MartinLautaroGimenez/estacion-meteorologica-estatica/models/Anemometer/images/4ff4661ae505d6dd8fcebf4c1d2a20cf.png

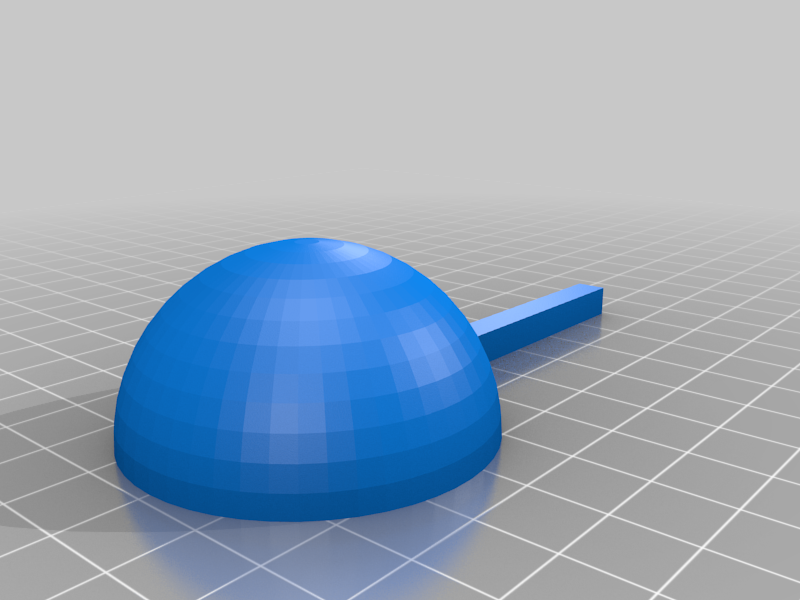
models/Anemometer/images/4ff4661ae505d6dd8fcebf4c1d2a20cf.png
