MartinLautaroGimenez/estacion-meteorologica-estatica/models/Anemometer/images/28f046effea293050f0cdabce47c510c.png

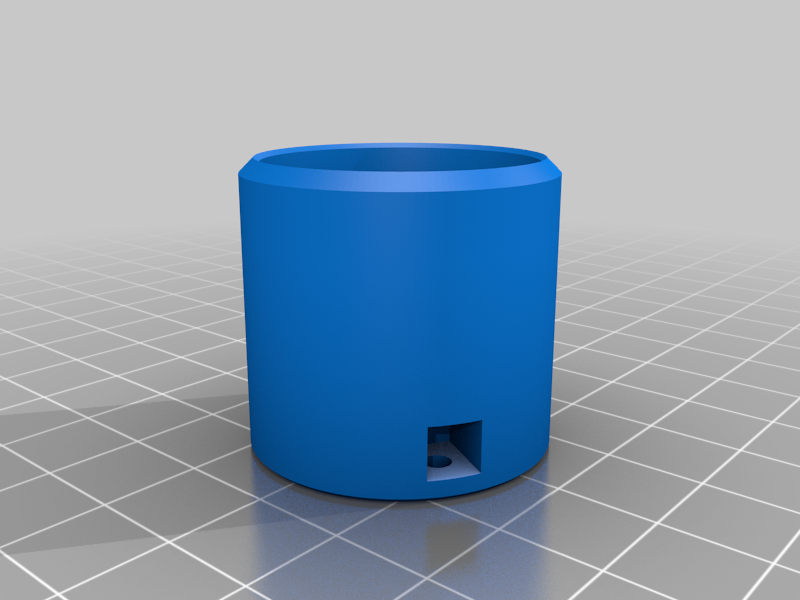
models/Anemometer/images/28f046effea293050f0cdabce47c510c.png
