MartinLautaroGimenez/estacion-meteorologica-estatica/models/Anemometer/images/anem.jpg

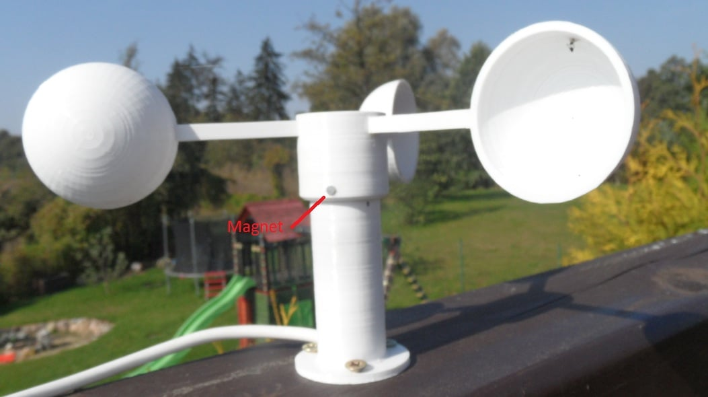
models/Anemometer/images/anem.jpg
