MartinLautaroGimenez/estacion-meteorologica-estatica/models/Anemometer/images/d6e86a1413bca8652d84cd858a84a04f.png

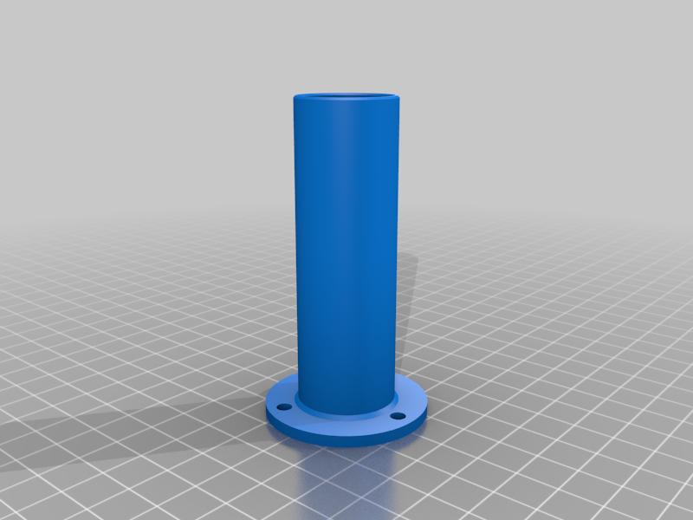
models/Anemometer/images/d6e86a1413bca8652d84cd858a84a04f.png
