MartinLautaroGimenez/estacion-meteorologica-estatica/models/Anemometer/images/hall_sensor.jpg

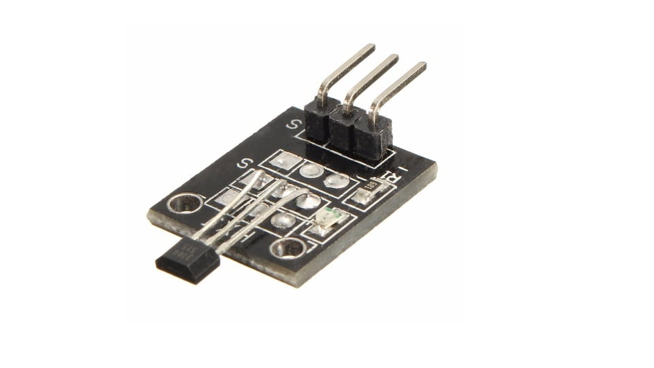
models/Anemometer/images/hall_sensor.jpg
