MartinLautaroGimenez/estacion-meteorologica-estatica/models/Anemometer/images/magnet.jpg

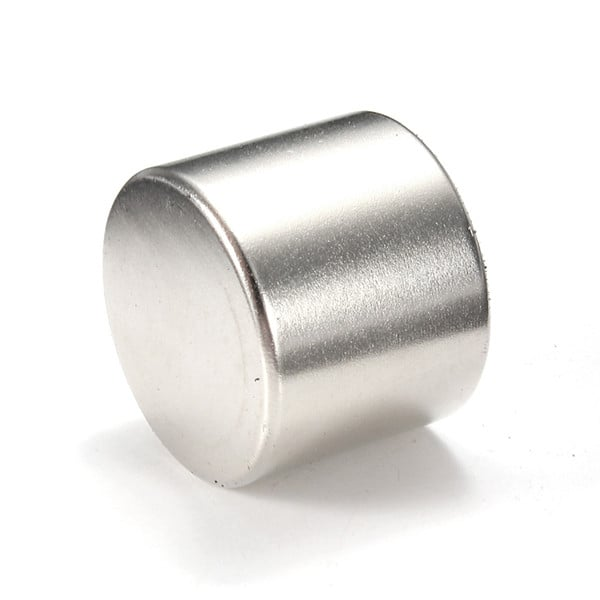
models/Anemometer/images/magnet.jpg
