MartinLautaroGimenez/estacion-meteorologica-estatica/Web/frontend/images/2025.jpg

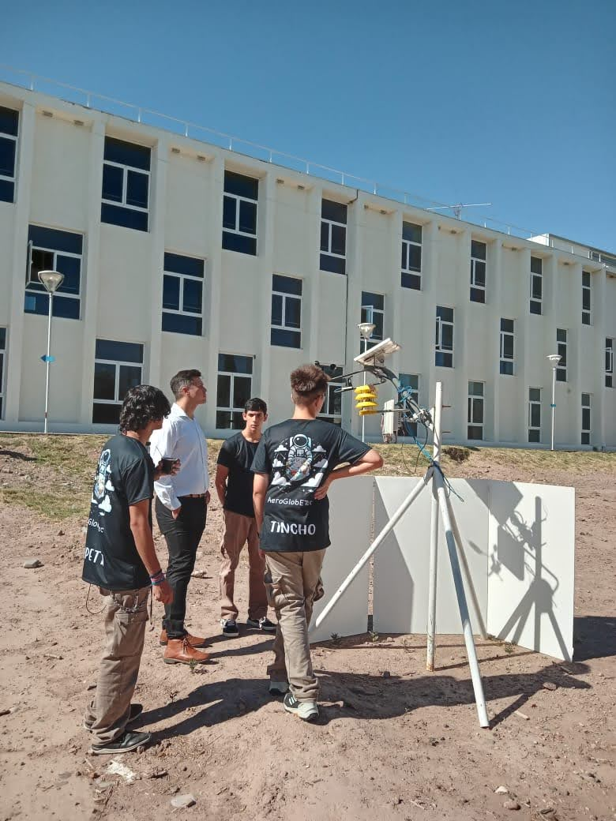
Web/frontend/images/2025.jpg
