MartinLautaroGimenez/estacion-meteorologica-estatica/Web/frontend/images/2025.png

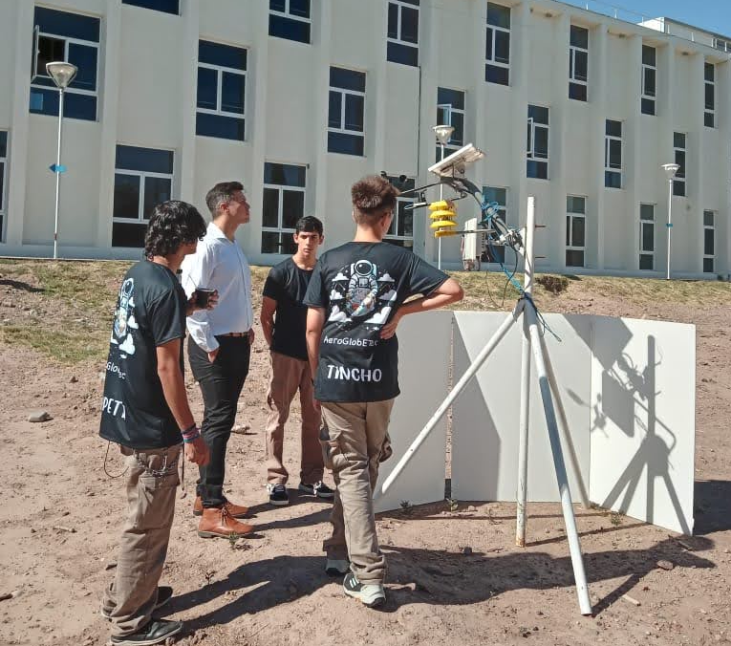
Web/frontend/images/2025.png
