MartinLautaroGimenez/estacion-meteorologica-estatica/Web/frontend/images/cate2023.jpeg

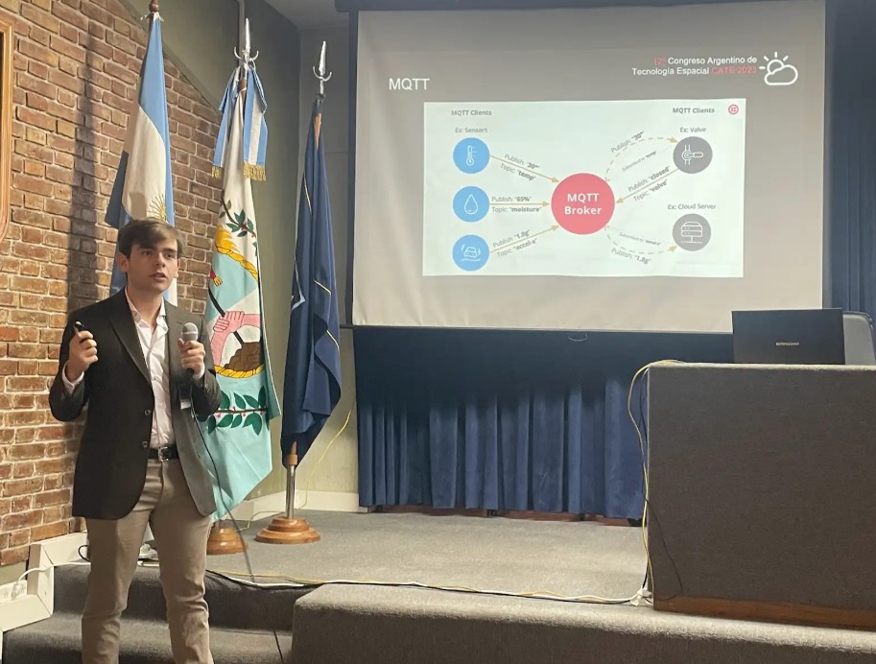
Web/frontend/images/cate2023.jpeg
