MartinLautaroGimenez/estacion-meteorologica-estatica/Web/frontend/images/eclipse.jpg

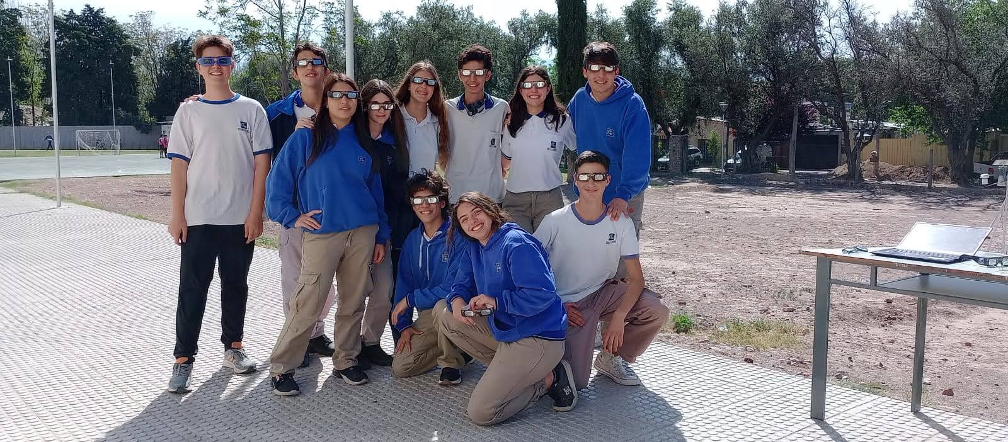
Web/frontend/images/eclipse.jpg
