MartinLautaroGimenez/estacion-meteorologica-estatica/Web/frontend/images/eme.jpeg

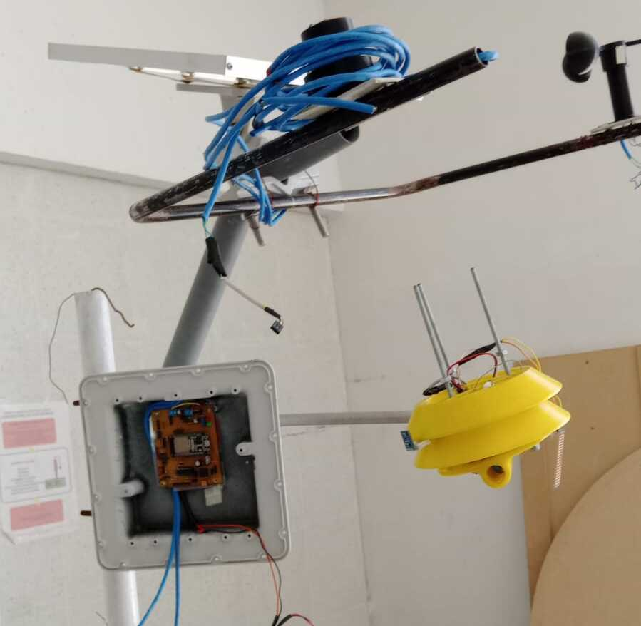
Web/frontend/images/eme.jpeg
