MartinLautaroGimenez/estacion-meteorologica-estatica/Web/frontend/images/eme.jpg

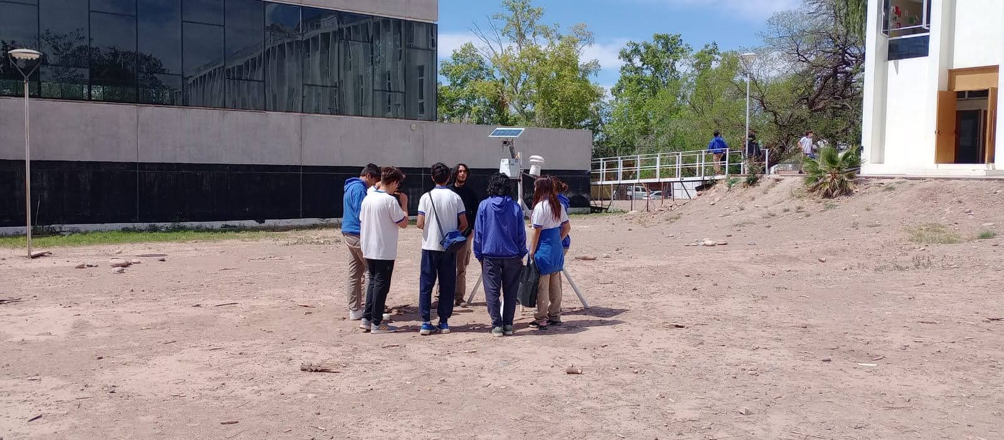
Web/frontend/images/eme.jpg
