MartinLautaroGimenez/estacion-meteorologica-estatica/Web/frontend/images/emebasica.jpeg

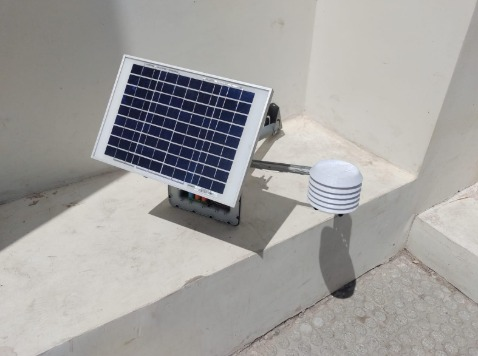
Web/frontend/images/emebasica.jpeg
