MartinLautaroGimenez/estacion-meteorologica-estatica/Web/frontend/images/emecompleta.jpeg

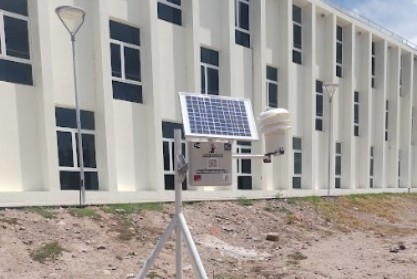
Web/frontend/images/emecompleta.jpeg
