MartinLautaroGimenez/estacion-meteorologica-estatica/Web/frontend/images/emm.jpeg

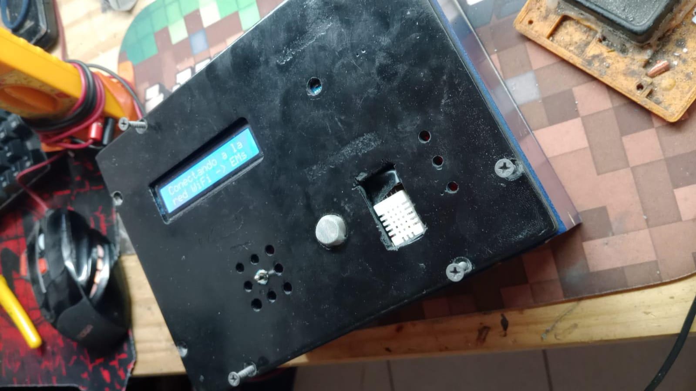
Web/frontend/images/emm.jpeg
