MartinLautaroGimenez/estacion-meteorologica-estatica/Web/frontend/images/heredar.jpg

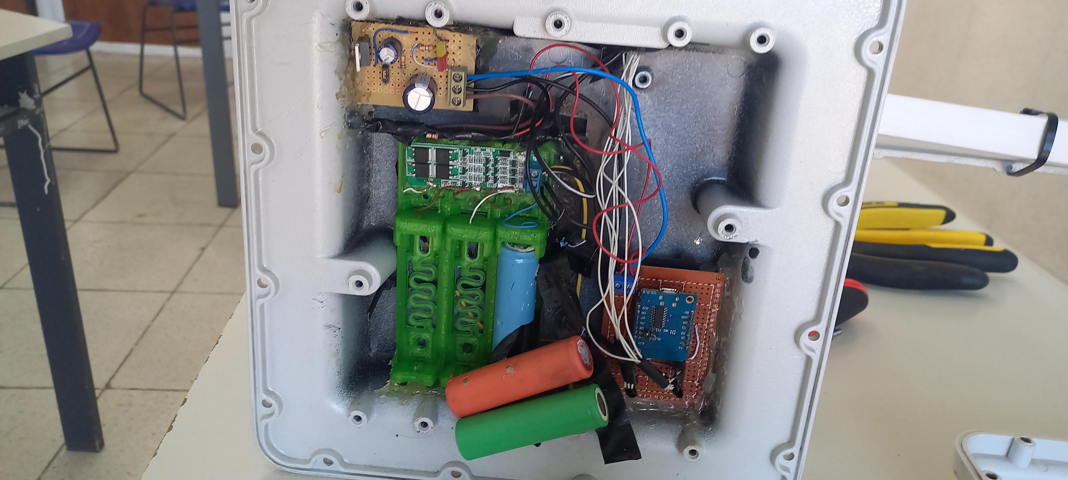
Web/frontend/images/heredar.jpg
