MartinLautaroGimenez/estacion-meteorologica-estatica/Web/frontend/images/nuestraeme.png

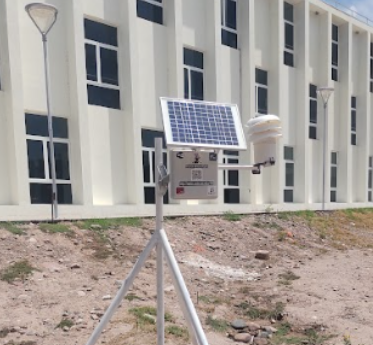
Web/frontend/images/nuestraeme.png
