MartinLautaroGimenez/estacion-meteorologica-estatica/Web/frontend/images/PIERRE.png

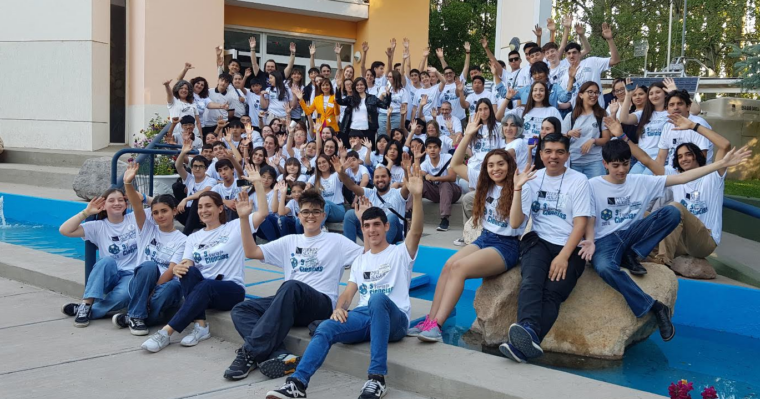
Web/frontend/images/PIERRE.png
