MartinLautaroGimenez/estacion-meteorologica-estatica/Web/frontend/images/sj.jpg

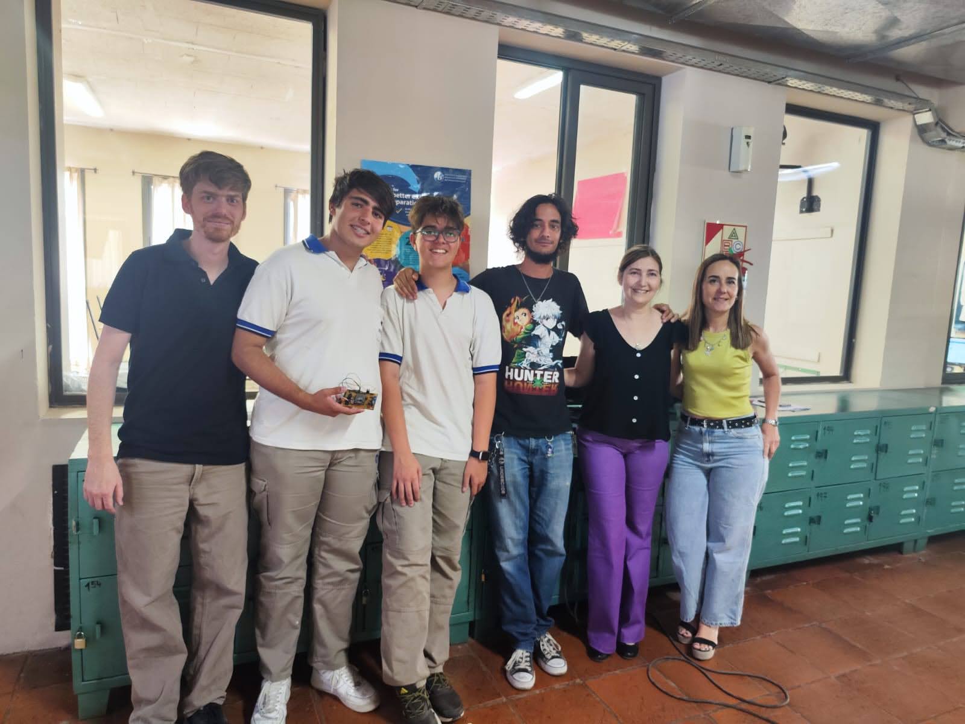
Web/frontend/images/sj.jpg
