MartinLautaroGimenez/estacion-meteorologica-estatica/Web/frontend/images/team/emecompleta.jpeg

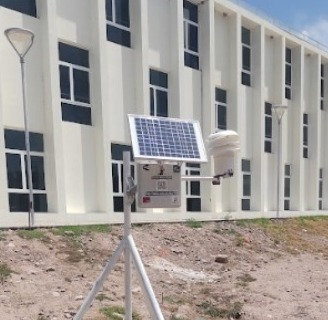
Web/frontend/images/team/emecompleta.jpeg
