MartinLautaroGimenez/estacion-meteorologica-estatica/Web/frontend/images/team/ivo.jpg

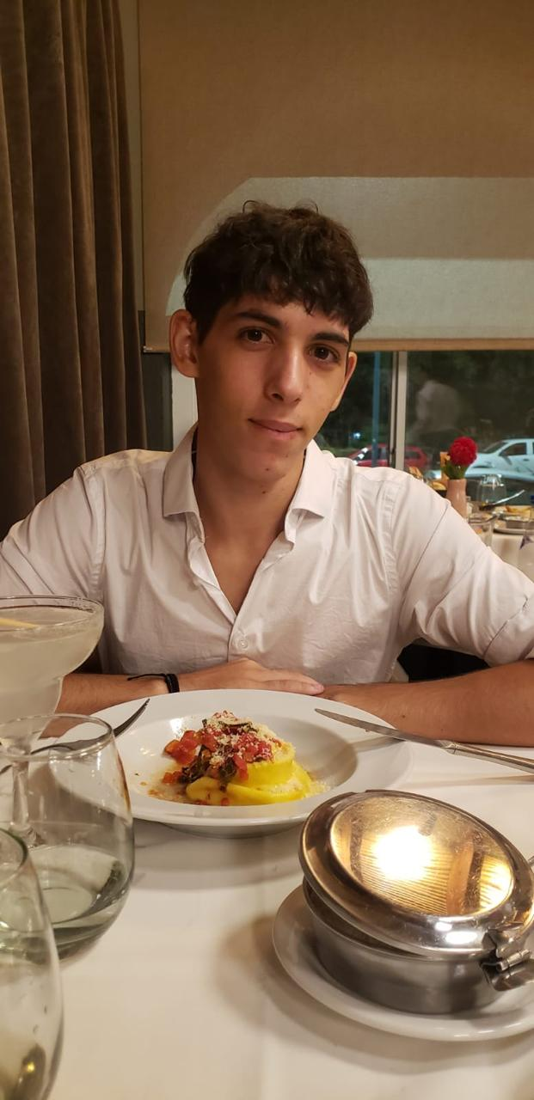
Web/frontend/images/team/ivo.jpg
