MartinLautaroGimenez/estacion-meteorologica-estatica/Web/frontend/images/team/Luis.jpg

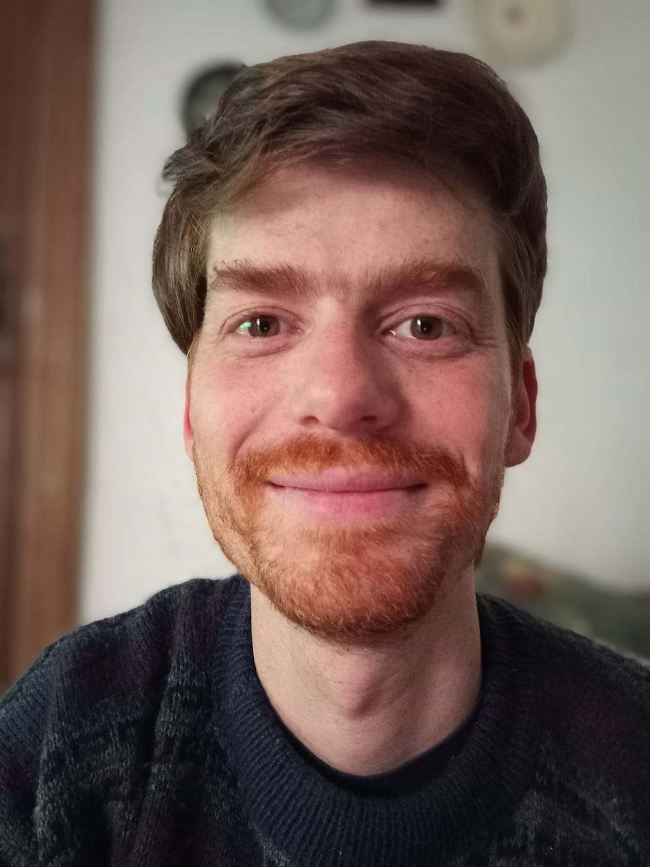
Web/frontend/images/team/Luis.jpg
