MartinLautaroGimenez/estacion-meteorologica-estatica/Web/frontend/images/team/mario.jpg

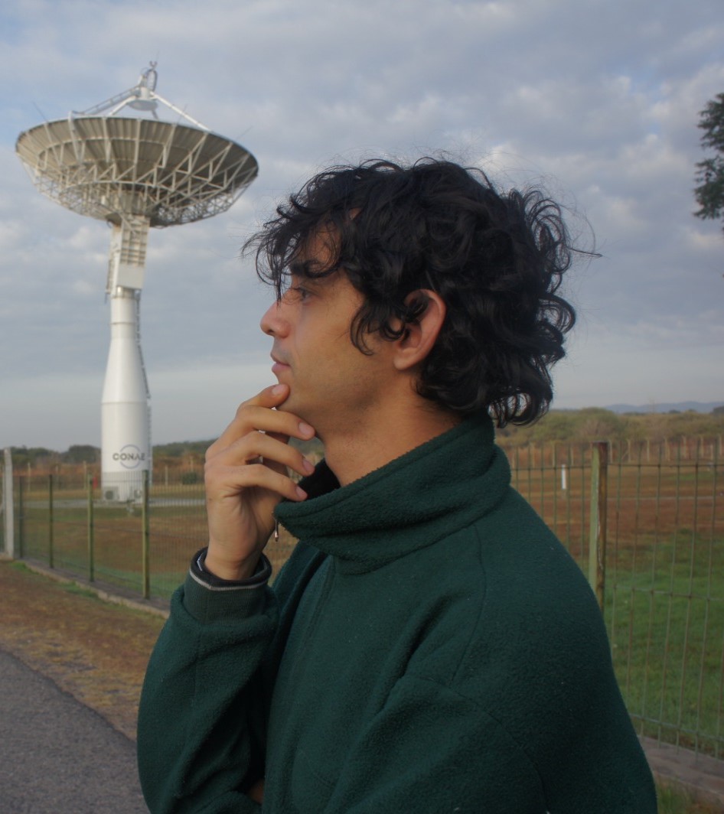
Web/frontend/images/team/mario.jpg
