MartinLautaroGimenez/estacion-meteorologica-estatica/Web/frontend/images/team/martin.jpg

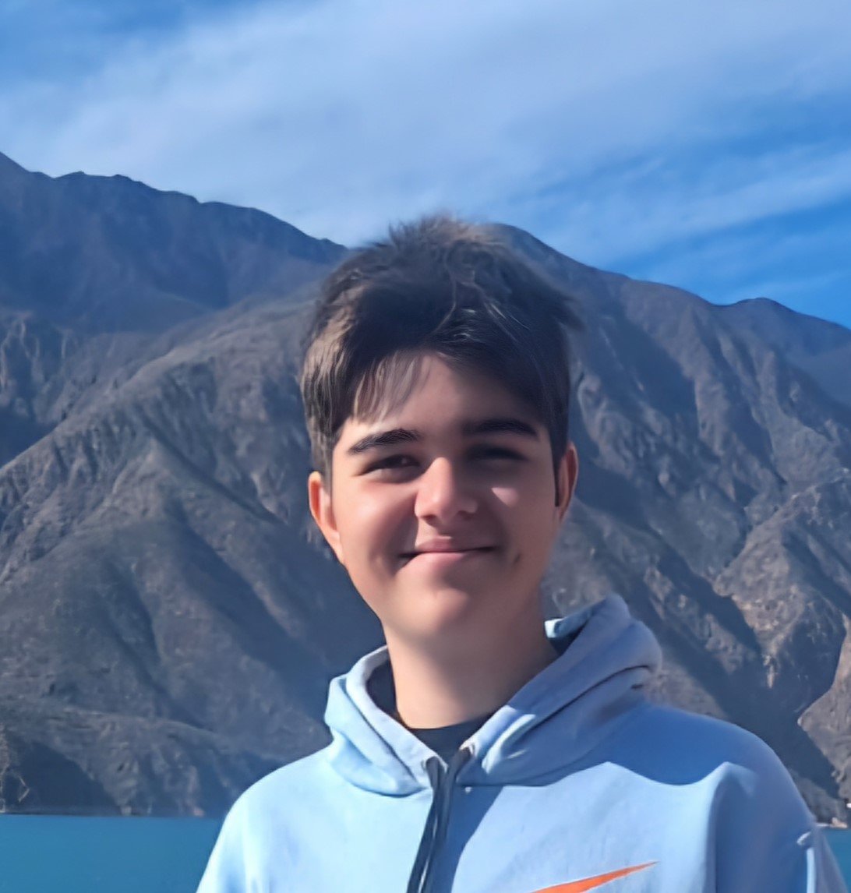
Web/frontend/images/team/martin.jpg
