MartinLautaroGimenez/estacion-meteorologica-estatica/Web/frontend/images/tucuman.jpg

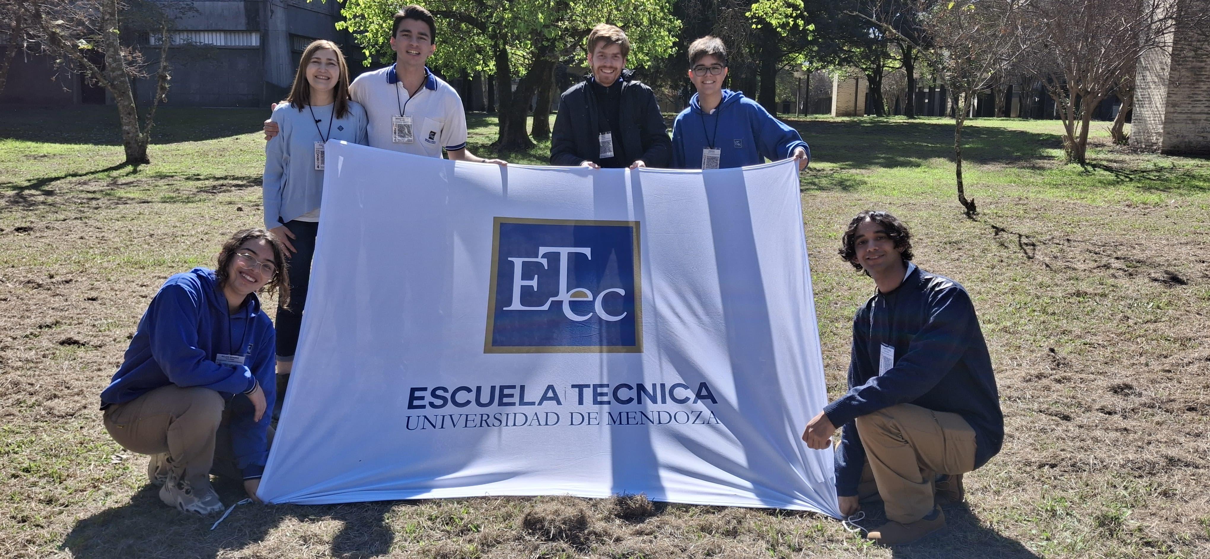
Web/frontend/images/tucuman.jpg
