MartinLautaroGimenez/estacion-meteorologica-estatica/Web/frontend/images/tucumanbalcon.jpeg

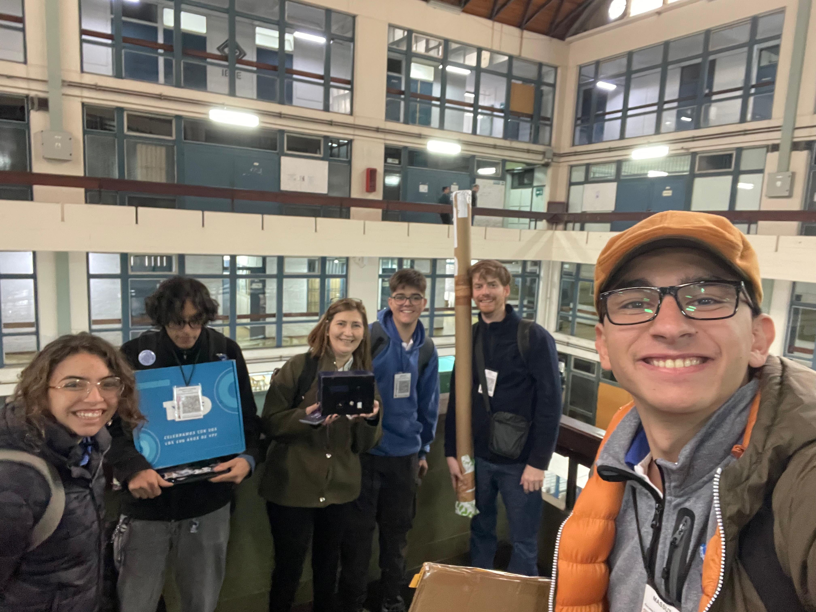
Web/frontend/images/tucumanbalcon.jpeg
