MartinLautaroGimenez/estacion-meteorologica-estatica/Src/mainSource/examples/mq135.cpp

#include <MQ135.h>
#include <Arduino.h>

/*  MQ135 gas sensor
    Datasheet can be found here: https://www.olimex.com/Products/Components/Sensors/SNS-MQ135/resources/SNS-MQ135.pdf

    Application
    They are used in air quality control equipments for buildings/offices, are suitable for detecting of NH3, NOx, alcohol, Benzene, smoke, CO2, etc

    Original creator of this library: https://github.com/GeorgK/MQ135
*/

#define PIN_MQ135 16  // El ejemplo menciona A2 pero tira error.

MQ135 mq135_sensor(PIN_MQ135);

float temperature = 21.0; // Assume current temperature. Recommended to measure with DHT22
float humidity = 25.0; // Assume current humidity. Recommended to measure with DHT22

void setup() {
  Serial.begin(9600);
}

void loop() {
  float rzero = mq135_sensor.getRZero();
  float correctedRZero = mq135_sensor.getCorrectedRZero(temperature, humidity);
  float resistance = mq135_sensor.getResistance();
  float ppm = mq135_sensor.getPPM();
  float correctedPPM = mq135_sensor.getCorrectedPPM(temperature, humidity);

  Serial.print("MQ135 RZero: ");
  Serial.print(rzero);
  Serial.print("\t Corrected RZero: ");
  Serial.print(correctedRZero);
  Serial.print("\t Resistance: ");
  Serial.print(resistance);
  Serial.print("\t PPM: ");
  Serial.print(ppm);
  Serial.print("\t Corrected PPM: ");
  Serial.print(correctedPPM);
  Serial.println("ppm");

  delay(300);
}
